Nitepone/uMFD/hw/blender/exports/button-v2.1.stl

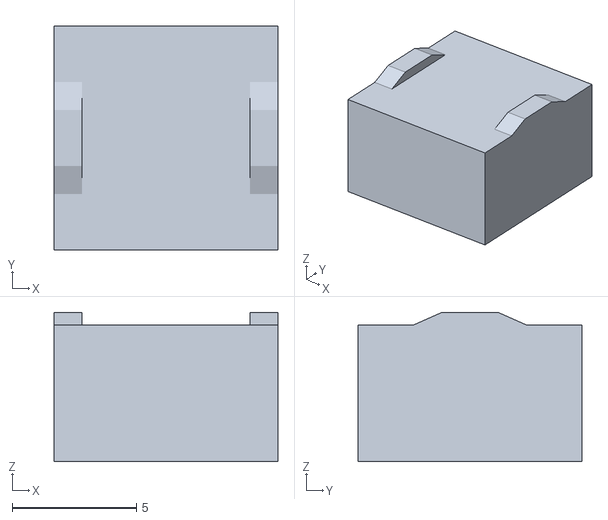
[picture p16: CAD file, 2025-04-08, an earlier design]
hw/blender/exports/button-v2.1.stl
9.00 x 9.00 x 6.00
