Nitepone/uMFD/hw/blender/exports/umfd-top-cover-v3.1.stl

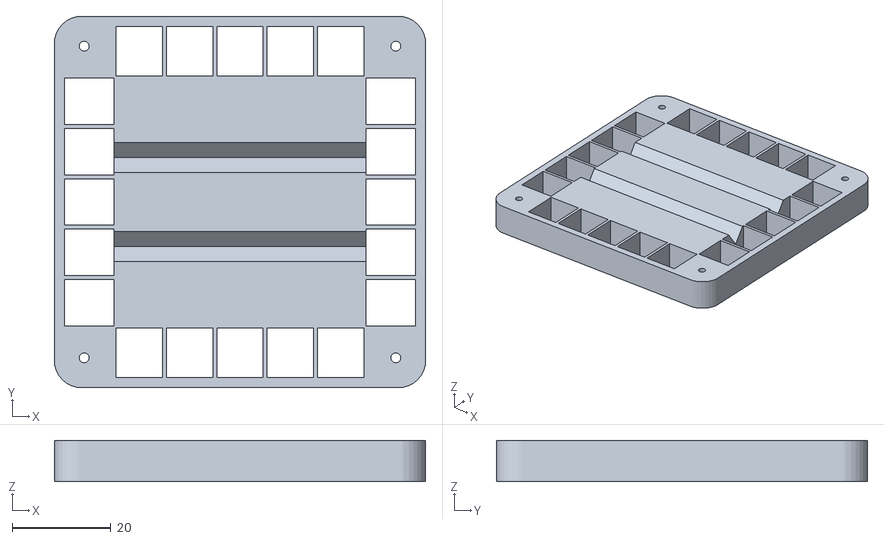
[picture p17: CAD file, 2025-04-08, an earlier design]
hw/blender/exports/umfd-top-cover-v3.1.stl
75.0 x 75.0 x 8.30
